PacketChat/MonkeyBadge/badge/main.py

from library.monkeybadge import MonkeyBadge


def main():
    """Entry point"""
    badge = MonkeyBadge()
    badge.run()


# Run the main function
if __name__ == "__main__":
    print("ENTRY")
    main()
